sergey12malyshev/SnakeGame/Case model/Case.bmp

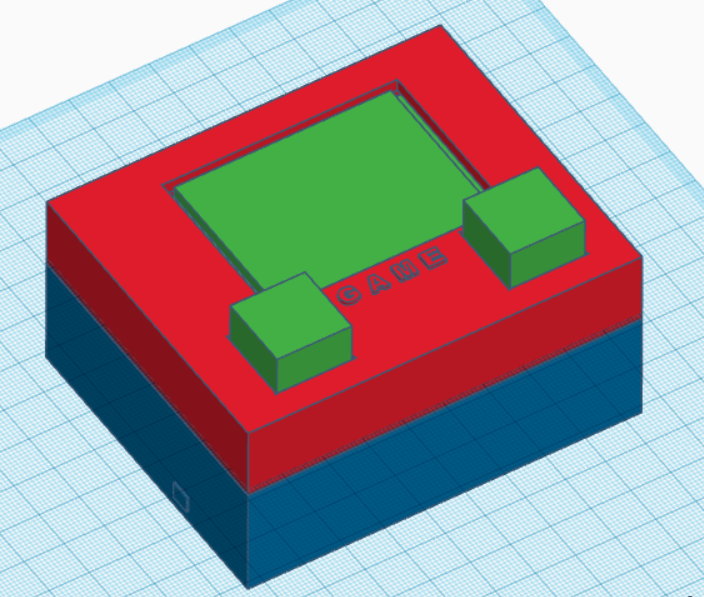
Case model/Case.bmp
