sergey12malyshev/SnakeGame/Case model/Case_transparent.bmp

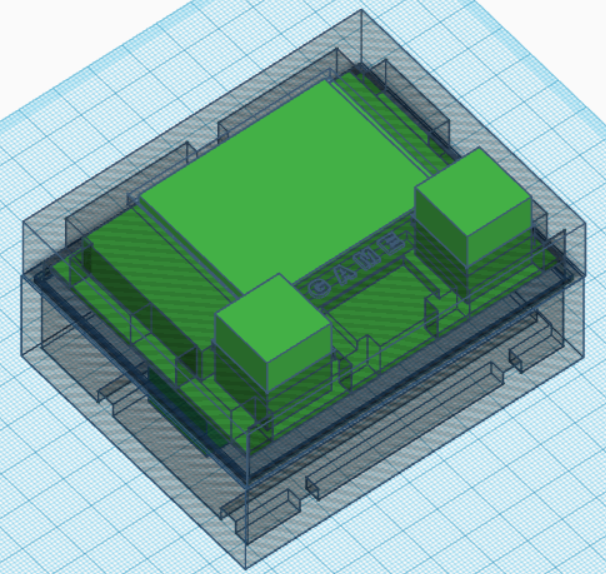
Case model/Case_transparent.bmp
