sergey12malyshev/SnakeGame/image/1688404908254.jpg

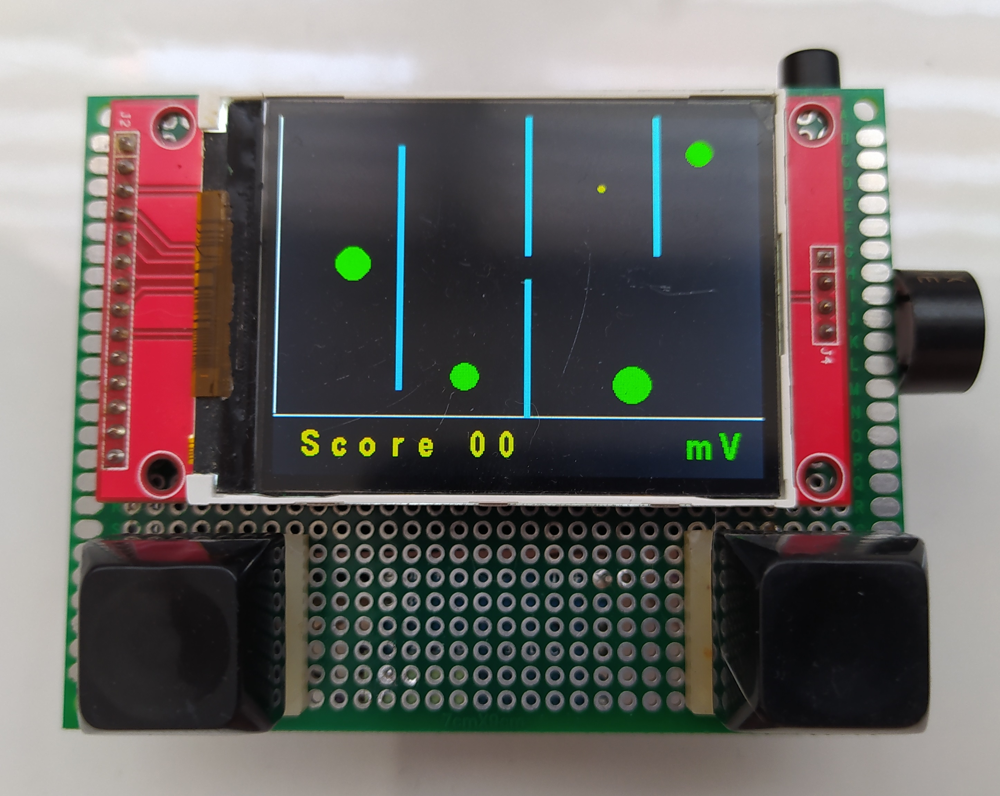
image/1688404908254.jpg
