sergey12malyshev/SnakeGame/image/1688404908262.jpg

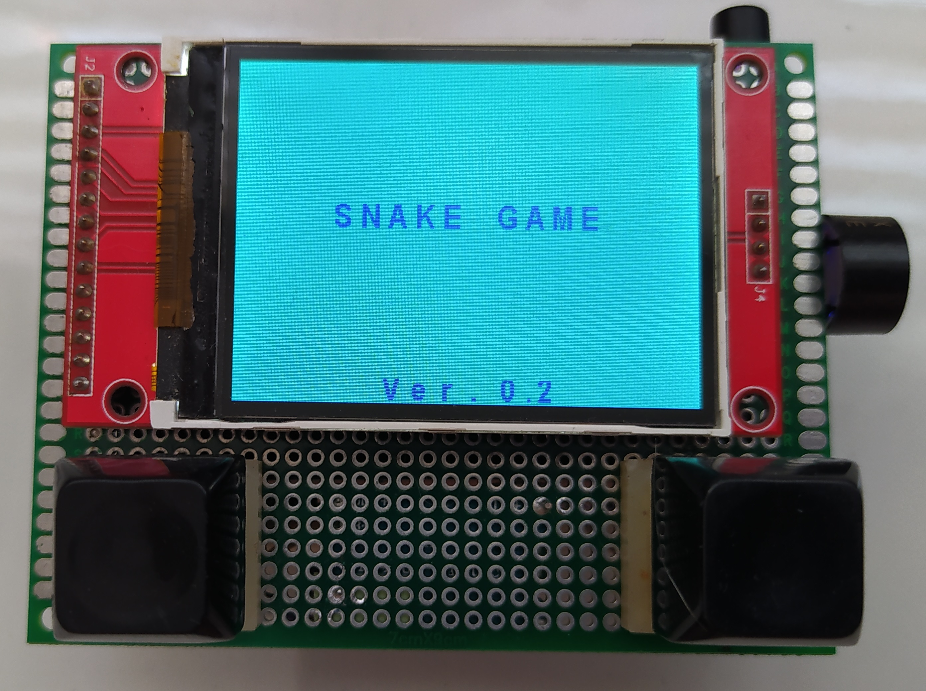
image/1688404908262.jpg
