sergey12malyshev/SnakeGame/Src/Screens.c

#include <stdint.h>
#include <stdbool.h>
#include <stdio.h>

#include "Screens.h"
#include "SPI_TFT.h"
#include "hard.h"
#include "Screens.h"
#include "main.h"
#include "colors.h"

/*X0*******************
 Y0
 *
 *
 *******************/

const unsigned char objets[][8]=
{
  {0x7C,0x02,0xC9,0x01,0x01,0xC9,0x02,0x7C},  // monster
  {0x00,0x42,0xA5,0x99,0x81,0x81,0x42,0x3C},  // Pac-man 1
  {0x00,0x42,0xE7,0xFF,0xFB,0xFF,0x7E,0x3C},  // Pac-man Left
  {0x3C,0x7E,0xFF,0xFB,0xFF,0xE7,0x42,0x00},  // Pac-man Right
  {0x3C,0x7E,0xFC,0xF8,0xF8,0xEC,0x7E,0x3C},  // Pac-man Up
  {0x3C,0x7E,0x3F,0x1F,0x1F,0x37,0x7E,0x3C},  // Pac-man Down
};

void createMonster(uint8_t object_number, uint16_t x0, uint16_t y0, uint16_t size, uint16_t fgcolor, uint16_t bgcolor)
{ // медленный алгоритм вывода
	for (int i = 0; i < 8; i++)
	{
		unsigned char temp = objets[object_number][i];

		for (unsigned char f = 0; f < 8; f++)
		{
			if ((temp >> f) & 0x01)
			{
				LCD_fillRect(x0 + i * size, y0 + f * size, size, size, fgcolor);
			}
			else
			{
				LCD_fillRect(x0 + i * size, y0 + f * size, size, size, bgcolor);
			}
		}
	}
}

void disableMonster(uint16_t x0, uint16_t y0, uint16_t size)
{ // медленный алгоритм закрашивания
	for (int i = 0; i < 8; i++)
	{
		for (unsigned char f = 0; f < 8; f++)
		{
			LCD_fillRect(x0 + i * size, y0 + f * size, size, size, getBlack());
		}
	}
}

void createPacman(uint16_t x0, uint16_t y0, int8_t direction_x, int8_t direction_y)
{
  const uint8_t size = 2;
  x0 -= 6; // отрисуем со смещением к центру
  y0 -= 6;

  if(direction_x == 0)
  {
    if(direction_y < 0)
    {
      createMonster(4U, x0, y0, size, getYellow(), getBlack());
    }
    else
    {
      createMonster(5U, x0, y0, size, getYellow(), getBlack());
    }
  }
  else
  {
    if(direction_x < 0)
    {
      createMonster(2U, x0, y0, size, getYellow(), getBlack());
    }
    else
    {
      createMonster(3U, x0, y0, size, getYellow(), getBlack());
    }
  }
}

void disablePacman(uint16_t x0, uint16_t y0)
{
  const uint8_t size = 2;
  x0 -= 6; // отрисуем со смещением к центру
  y0 -= 6;

  disableMonster(x0, y0, size);
}

void createFood(uint16_t x0, uint16_t y0, const uint16_t sizeFood)
{
  fillCircle(x0, y0, sizeFood, getGreen());
}

void deleteFood(uint16_t x0, uint16_t y0, const uint16_t sizeFood)
{
  fillCircle(x0, y0, sizeFood, getBlack());
  scoreIncrement();
}

void createWalls(uint16_t x0, uint16_t y0, uint16_t x1, uint16_t y1, uint16_t size)
{
  H_line(x0, y0, x1, y1, size, getBlue());
}

void createWorkRegion(void)
{
  LCD_Fill(getBlack());
  line(0, 201, 319, 201, getWhite());
  line(0, 0, 0, 199, getWhite());
  STRING_OUT("Score", 10, 210, 1, getWhite(), getBlack());
  STRING_OUT("%", 270, 210, 1, getGreen(), getBlack());
  batterySumbolShow();
}

void screenBootProcess(void)
{
  extern const int16_t SWversionMajor, SWversionMinor, SWversionPatch;
  extern const char HWversion[];
  const uint16_t colorBg = getBlack();
  LCD_Fill(colorBg);
  simple_font_string_OUT("GAME BOX", 30, 50, 2, getBlue(), colorBg);
  char buf[12] = {0};
  sprintf(buf,"SW ver.: %d.%d.%d", SWversionMajor, SWversionMinor, SWversionPatch);
  simple_font_string_OUT(buf, 30, 100, 2, getWhite(), colorBg);
  sprintf(buf,"HW ver.: %s", HWversion);
  simple_font_string_OUT(buf, 30, 125, 2, getWhite(), colorBg);
  HAL_Delay(120);
  simple_font_string_OUT("Booting...", 30, 150, 2, getWhite(), colorBg);
  HAL_Delay(155);
  simple_font_string_OUT("Run sound test...", 30, 175, 2, getWhite(), colorBg);
}

void screenSaver(void)
{
  extern const int16_t SWversionMajor, SWversionMinor;
  const uint16_t colorBg = getBlack();
  LCD_Fill(colorBg);
  STRING_OUT("GAME BOX", 90, 110, 10, getBlue(), colorBg);
  STRING_OUT("2024 MSE", 100, 220, 5, 0x00FF, colorBg);

  createMonster(0, 50, 50, 5, getRed(), colorBg);
  createMonster(1, 200, 150, 5, getOrange(), colorBg);
  createMonster(0, 195, 45, 5, getBlack(), COLOR(0, 0, 255));
}

void stringGameOver(void)
{
  STRING_OUT("GAME OVER", 85, 100, 3, 0x00FF, getBlack());
}

void screenEndGame(void)
{
  LCD_Fill(getOrange());
  STRING_OUT("GAME OVER", 85, 100, 3, 0x00FF, getOrange());
  STRING_OUT(">", 290, 210, 1, 0x00FF, getGreen());
  STRING_OUT("Go", 235, 210, 1, 0x00FF, getOrange());
  STRING_OUT("<", 10, 210, 1, 0x00FF, getGreen());
  STRING_OUT("Menu", 40, 210, 1, 0x00FF, getOrange());
}

void screenGameCompleted(void)
{
  const uint16_t colorBg = COLOR(43, 217, 46);
  LCD_Fill(colorBg);
  STRING_OUT("Next Level!", 100, 140, 3, 0x00FF, colorBg);
  STRING_OUT(">", 290, 210, 1, 0x00FF, getGreen());
}

void screenOverVoltageError(void)
{
  LCD_Fill(getRed());
  STRING_OUT("OVERVOLTAGE!", 80, 180, 3, getWhite(), getRed());
}

void screenUnderVoltageError(void)
{
  LCD_Fill(getRed());
  STRING_OUT("UNDERVOLTAGE!", 80, 180, 3, getWhite(), getRed());
}

void batterySumbolShow(void)
{
  const uint8_t x_min = 206;
  const uint8_t y_min = 208;
  const uint8_t y_max = 233;

  line(x_min, y_min, 290, y_min, getGreen());
  line(x_min, y_max, 290, y_max, getGreen());
  line(x_min, y_min, x_min, y_max, getGreen());

  line(290, y_min, 290, y_min + 5, getGreen());
  line(290, y_max - 5, 290, y_max, getGreen());

  line(290, y_min + 5, 295, y_min + 5, getGreen());
  line(290, y_max - 5, 295, y_max - 5, getGreen());

  line(295, y_max - 5, 295, y_min + 5, getGreen());
}

void scoreUpdate(uint16_t scoreLoc)
{
  STRING_NUM_L(scoreLoc, 2, 120, 210, getWhite(), getBlack());  
}
